jondurrant/RPIPicoWeatherStation/src/StatusAgent.cpp

/*
 * StatusAgent.cpp
 *
 *  Created on: 15 Aug 2024
 *      Author: jondurrant
 */

#include "StatusAgent.h"
#include <cstdio>

StatusAgent * StatusAgent::pSelf = NULL;

StatusAgent::StatusAgent(
		uint8_t swt,
		uint8_t red,
		uint8_t grn,
		uint8_t blu
		){
	uint slicer;
	xSWT = swt;
	xRED = red;
	xGRN = grn;
	xBLU = blu;

	if (xSWT <= 28){
		gpio_init(xSWT);
		gpio_set_dir(xSWT, GPIO_IN);
		gpio_pull_up(xSWT);

		gpio_set_irq_enabled_with_callback(
				xSWT,
			   GPIO_IRQ_EDGE_FALL,
			   true,
			   StatusAgent::gpio_callback
			   );
	}

	if (xRED <= 28){
		gpio_init(xRED);
		slicer = pwm_gpio_to_slice_num(xRED);
		gpio_set_function(xRED, GPIO_FUNC_PWM);
		pwm_set_enabled(slicer, true);
		//gpio_set_dir(xRED, GPIO_OUT);
		pwm_set_gpio_level (xRED, 0 );
	}

	if (xGRN <= 28){
		gpio_init(xGRN);
		slicer = pwm_gpio_to_slice_num(xGRN);
		gpio_set_function(xGRN, GPIO_FUNC_PWM);
		pwm_set_enabled(slicer, true);
		//gpio_set_dir(xGRN, GPIO_OUT);
		pwm_set_gpio_level (xGRN, 0 );
	}

	if (xBLU <= 28){
		gpio_init(xBLU);
		slicer = pwm_gpio_to_slice_num(xBLU);
		gpio_set_function(xBLU, GPIO_FUNC_PWM);
		pwm_set_enabled(slicer, true);
		//gpio_set_dir(xBLU, GPIO_OUT);
		pwm_set_gpio_level (xBLU, 0 );
		//printf("BLU %u slicer %u\n", xBLU, slicer);
	}

	StatusAgent::pSelf= this;
}

StatusAgent::~StatusAgent() {
	// NOP
}

StatusAgent * StatusAgent::getInstance(){
	return pSelf;
}

configSTACK_DEPTH_TYPE StatusAgent::getMaxStackSize(){
	return 256;
}

void StatusAgent::run(){
	bool lastSwtState = false;
	for (;;){

		if (xSWT > 28) {
			displayStatus( xStatus);
		} else {
			bool swtState = gpio_get(xSWT);
			if (swtState != lastSwtState){
				lastSwtState = swtState;

				if (!swtState){
					displayStatus( xStatus);
				} else {
					displayStatus( 0x00);
				}
			}
		}
		vTaskDelay(1000);
	}
}

void StatusAgent::displayStatus(uint32_t status){
	uint16_t blu = status & 0xFF;
	blu = blu * blu;
	if (xBLU <= 28){
		pwm_set_gpio_level (xBLU,  blu);
	}

	uint16_t grn = (status & 0xFF00) >> 8;
	grn = grn * grn;
	if (xGRN <= 28){
		pwm_set_gpio_level (xGRN,  grn);
	}

	uint16_t red = (status & 0xFF0000) >> 16;
	red = red * red;
	if (xRED <= 28){
		pwm_set_gpio_level (xRED,  red);
	}

	//printf("Displayed(%d,%d,%d) %X %X %X\n", xRED, xGRN, xBLU,  red, grn, blu);
}


void StatusAgent::setStatus(uint32_t rgb){
	xStatus = rgb;

	if (xSWT > 28) {
		displayStatus( xStatus);
	}
}


void StatusAgent::gpio_callback(uint gpio, uint32_t events){
	//NOP
}

void StatusAgent::setOnline(){
	setStatus(0x000000FF);
}
void StatusAgent::setOffline(){
	setStatus(0x0000FF00);
}
void StatusAgent::setWake(){
	setStatus(0x00FFFFFF);
}
void StatusAgent::setSleep(){
	setStatus(0x001F1F1F);
}
void StatusAgent::setOK(){
	setStatus(0x0000FF00);
}
void StatusAgent::setFault(){
	setStatus(0x00FFFF00);
}
void StatusAgent::setFatal(){
	setStatus(0x00FF0000);
}
