jondurrant/RPIPicoWeatherStation/src/WeatherStationPayload.h

/*
 * WeatherStationPayload.h
 *
 *  Created on: 12 Sept 2024
 *      Author: jondurrant
 */

#ifndef SRC_WEATHERSTATIONPAYLOAD_H_
#define SRC_WEATHERSTATIONPAYLOAD_H_

#include "JSONSerialisable.h"
#if CPPUTEST_USE_NEW_MACROS
   #undef new
#endif
#include <map>
#if CPPUTEST_USE_NEW_MACROS
   #include "CppUTest/MemoryLeakDetectorNewMacros.h"
#endif
#include "PayloadPart.h"
#include <string>
#include "RTCStatus.h"

#ifndef WS_PAYLOAD_LEN
#define WS_PAYLOAD_LEN 2048
#endif

class WeatherStationPayload  :
		public JSONSerialisable,
		public PayloadPart {
public:
	WeatherStationPayload(RTCStatus * rtc);
	WeatherStationPayload( );
	virtual ~WeatherStationPayload();

	virtual char * json();

	virtual char* writeJson( char* dest, const char * name, size_t* remLen );

	void addPart(const char * name, PayloadPart * p);

private:
	char xBuffer[WS_PAYLOAD_LEN];

	std::map<std::string,  PayloadPart *> xPayloadParts;

	RTCStatus *  pRTC;

};

#endif /* SRC_WEATHERSTATIONPAYLOAD_H_ */
